Bauteiltoeter/wled_hardware/measurements/DS4_QuickPrint11.png

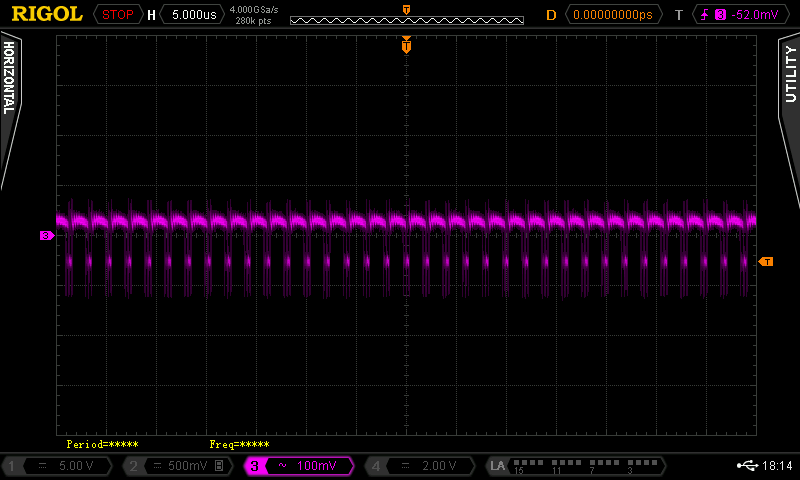
measurements/DS4_QuickPrint11.png
