Bauteiltoeter/wled_hardware/measurements/ac_switch_200mA_21V_2.png

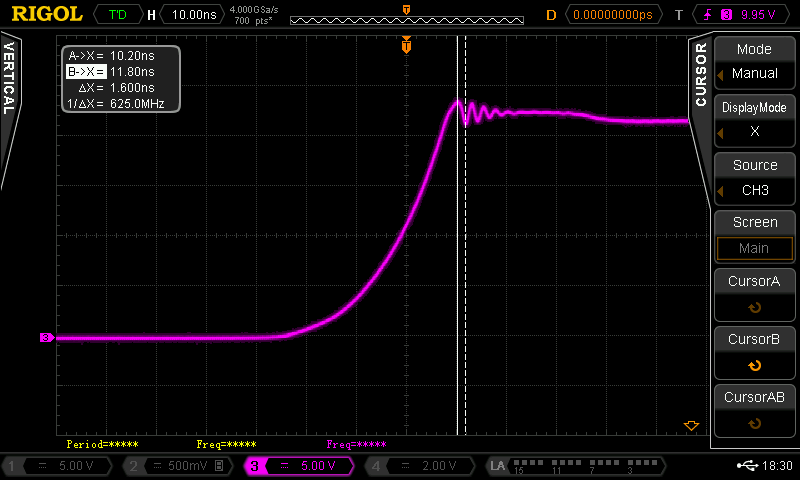
measurements/ac_switch_200mA_21V_2.png
