Bauteiltoeter/wled_hardware/measurements/feedback_1.png

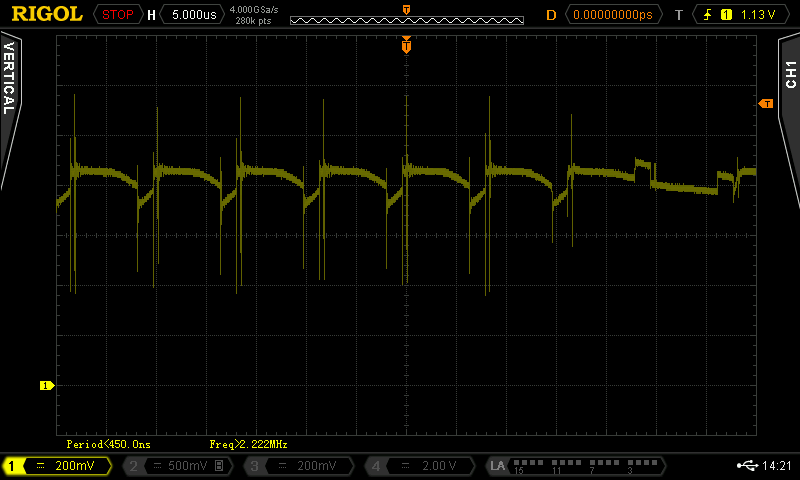
measurements/feedback_1.png
