Bauteiltoeter/wled_hardware/measurements/feedback_2.png

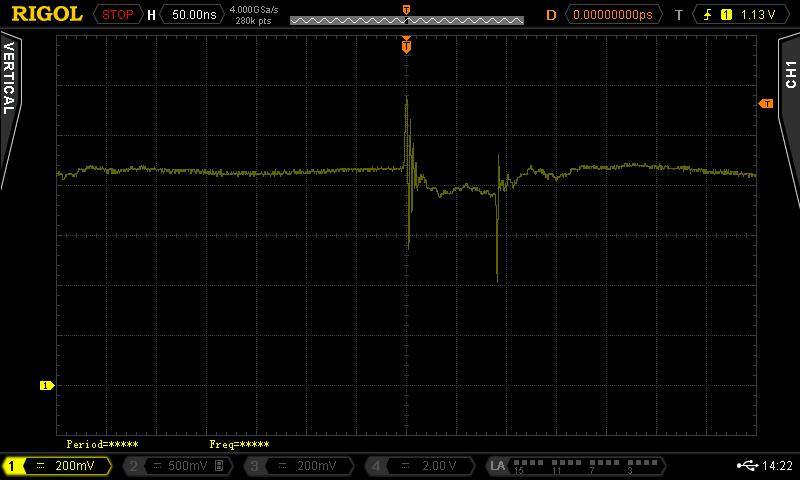
measurements/feedback_2.png
