Bauteiltoeter/wled_hardware/measurements/feedback_3.png

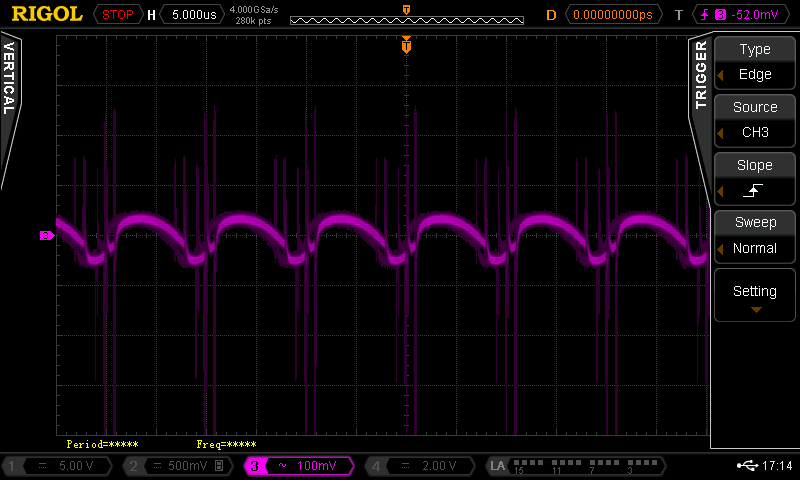
measurements/feedback_3.png
