Bauteiltoeter/wled_hardware/measurements/input_200mA_21V.png

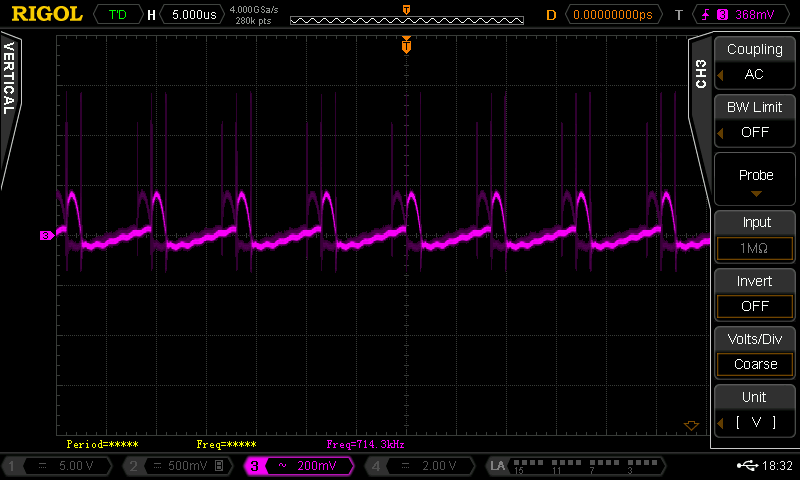
measurements/input_200mA_21V.png
