Bauteiltoeter/wled_hardware/measurements/input_200mA_21V_2.png

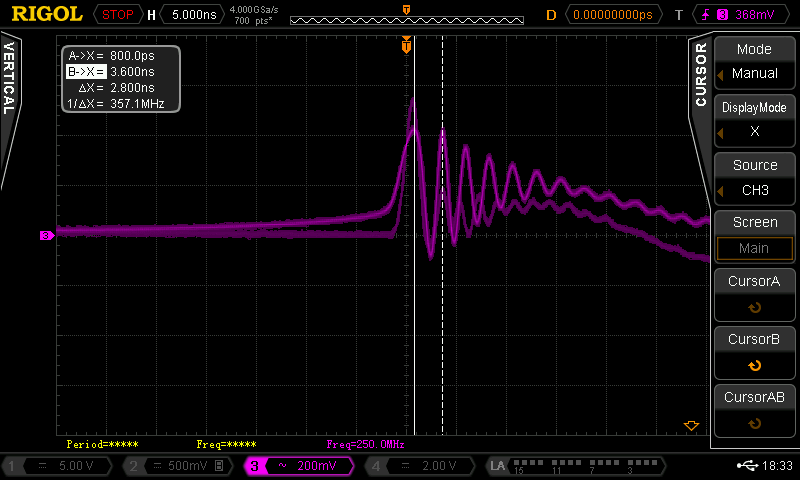
measurements/input_200mA_21V_2.png
