Bauteiltoeter/wled_hardware/measurements/output_3.png

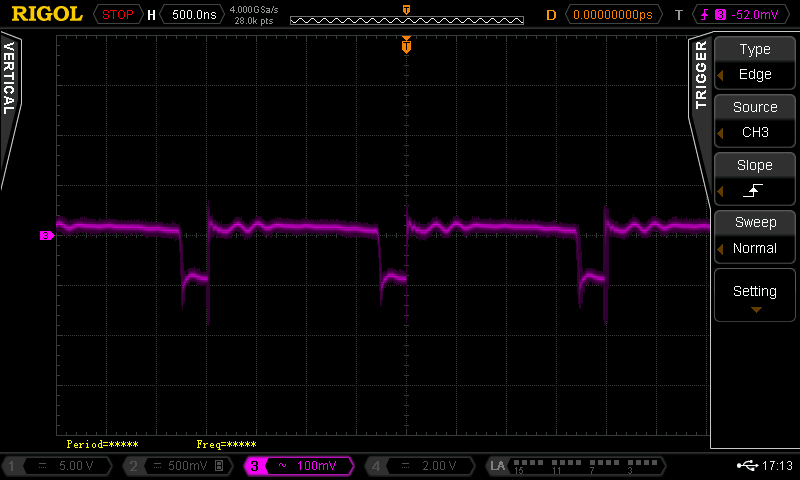
measurements/output_3.png
