Bauteiltoeter/wled_hardware/measurements/output_200mA_19V.png

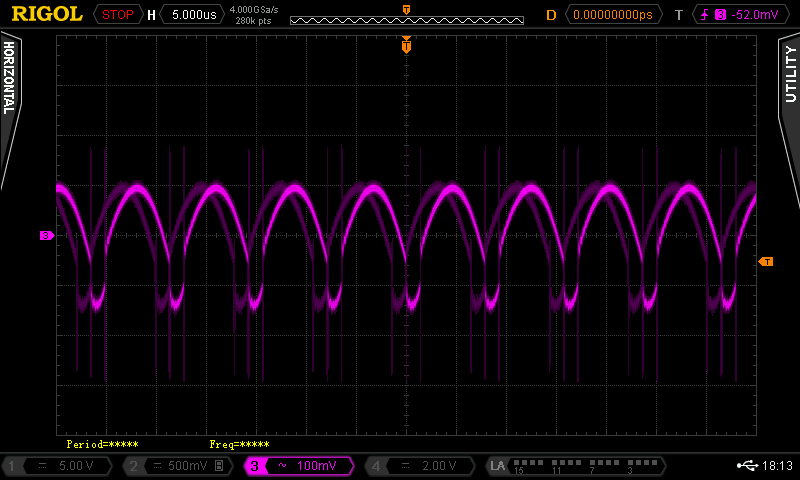
measurements/output_200mA_19V.png
