Bauteiltoeter/wled_hardware/measurements/output_800mA_21V.png

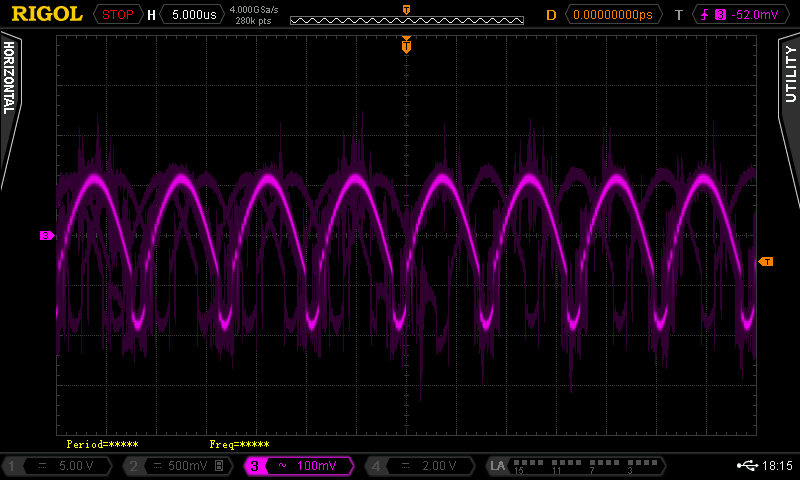
measurements/output_800mA_21V.png
